MOSH-Insa-Toulouse/Graphite_2022_GUICHANE_BENIMELIS/LTSpice/capteur.asc

B1: bi; I=V(cp,cn)*({G0}+v(gc,gn)*{G0})
C1: cap; {C0}
R1: res; {R0}
Named nets: gp, gn, gc, cn, cp
