MOSH-Insa-Toulouse/Graphite_2022_GUICHANE_BENIMELIS/LTSpice/CAPTEUR_GRAPHITE.asc

C1: cap; 100n
C2: cap; 100n
C3: cap; 1p
C4: cap; 1µ
R1: res; 100k
R2: res; 1k
R3: res; 100k
R5: res; 10k
R6: res; 1k
U1: LTC1050
V1: voltage; 5
V2: voltage; SINE(0 325 50)
V3: voltage; PULSE(0 1 0.2 0.1 0.1 20); AC 1 0
X1: Draft1
Named nets: 0, ADC
.param G0=10n R0=100k C0=200p
;tran 4
.ac dec 100 1 100k
